jbrazio/arduheater/arduheater/console.h

/**
 * Arduheater - An intelligent dew buster for astronomy
 * Copyright (C) 2016-2019 João Brázio [joao@brazio.org]
 *
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
 */

#ifndef __LOG_H__
#define __LOG_H__

#include <stdint.h>
#include <stdlib.h>

#include "version.h"
#include "config.h"

#include <avr/pgmspace.h>

#include "serial.h"

// Special characters
const char string_colon   [] PROGMEM = { 0x3a, 0x00 };
const char string_comma   [] PROGMEM = { 0x2c, 0x00 };
const char string_eol     [] PROGMEM = { 0x0a, 0x00 };
const char string_minus   [] PROGMEM = { 0x2d, 0x00 };
const char string_percent [] PROGMEM = { 0x25, 0x00 };
const char string_space   [] PROGMEM = { 0x20, 0x00 };
const char string_zero    [] PROGMEM = { 0x30, 0x00 };

class Log
{
  /**
   * Disable the creation of an instance of this object.
   * This class should be used as a static class.
   */
  private:
     Log() {;}
    ~Log() {;}

  public:
    static void eol()   { Log::PGM(string_eol); }
    static void space() { Log::PGM(string_space); }
    static void comma() { Log::PGM(string_comma); }
    static void colon() { Log::PGM(string_colon); }
    static void minus() { Log::PGM(string_minus); }
    static void zero()  { Log::PGM(string_zero); }

  public:
    inline static void string(const char* s)
    {
      while (*s)
        Serial::write(*s++);
    }

    inline static void PGM(const char* s)
    {
      char c;
      while ((c = pgm_read_byte(s++)))
        Serial::write(c);
    }

  public:
    // uint8: 0 to 255
    static void number(const uint8_t& n)
    {
      uint8_t digits = 3;
      if (n < 10) { digits = 1; }
      else if (n < 100) { digits = 2; }
      Log::number(n, 10, digits);
    }

    // int8: -127 to 127
    static void number(const int8_t& n)
    {
      if (n < 0) {
        Log::minus();
        Log::number(-n, 10);
      } else Log::number(n);
    }

    // uint16: 0 to 65535
    static void number(const uint16_t& n)
    {
      Log::number(n, 10);
    }

    // int16: -32768 to 32767
    static void number(const int16_t& n)
    {
      if (n < 0) {
        Log::minus();
        Log::number(-n, 10);
      } else Log::number(n, 10);
    }

    // uint32: 0 to 4294967295L
    static void number(const uint32_t& n)
    {
      Log::number(n, 10);
    }

    // int32: -2147483648L to 2147483647L
    static void number(const int32_t& n)
    {
      if (n < 0) {
        Log::minus();
        Log::number(-n, 10);
      } else Log::number(n, 10);
    }

    // float:
    static void number(const float& n)
    {
      Log::fraq(n, 2);
    }

  public:
    static void binary(const uint8_t& n)  { Log::number(n, 2, 8); }
    static void binary(const int8_t& n)   { Log::number(n, 2, 8); }
    static void binary(const uint16_t& n) { Log::number(n, 2, 16); }
    static void binary(const int16_t& n)  { Log::number(n, 2, 16); }
    static void binary(const uint32_t& n) { Log::number(n, 2, 32); }
    static void binary(const int32_t& n)  { Log::number(n, 2, 32); }

  protected:
    static void number(uint32_t n, const uint8_t& base, const uint8_t& digits)
    {
      uint8_t i = 0;
      unsigned char buf[digits];

      for (; i < digits; i++) {
        buf[i] = n % base;
        n /= base;
      }

      for (; i > 0; i--) {
        if (i < digits && base == 2 && !((digits - i) % 4)) Log::space();
        Serial::write('0' + buf[i - 1]);
      }
    }

    static void number(const uint32_t& n, const uint8_t& base)
    {
      if (!n) {
        Log::zero();
        return;
      }

      uint32_t c = n;
      uint8_t digits = 0;
      while (c) { c /= 10; digits++; }
      Log::number(n, base, digits);
    }

    static void fraq(float n, const uint8_t& decimal_places)
    {
      if (n < 0) {
        Log::minus();
        n = -n;
      }

      uint8_t decimals = decimal_places;

      // Quickly convert values expected to be E0 to E-4.
      while (decimals >= 2) {
        n *= 100;
        decimals -= 2;
      }

      if (decimals) { n *= 10; }
      n += 0.5; // Add rounding factor. Ensures carryover through entire value.

      // Generate digits backwards and store in string.
      unsigned char buf[10];
      uint8_t i = 0;
      uint32_t a = (long)n;

      // Place decimal point, even if decimal places are zero.
      buf[decimal_places] = '.';

      while(a > 0) {
        if (i == decimal_places) { i++; } // Skip decimal point location
        buf[i++] = (a % 10) + '0'; // Get digit
        a /= 10;
      }

      // Fill in zeros to decimal point for (n < 1)
      while (i < decimal_places)
        buf[i++] = '0';

      // Fill in leading zero, if needed.
      if (i == decimal_places) {
        i++;
        buf[i++] = '0';
      }

      // Console the generated string.
      for (; i > 0; i--)
        Serial::write(buf[i-1]);
    }
};

class LogLn
{
  /**
   * Disable the creation of an instance of this object.
   * This class should be used as a static class.
   */
  private:
     LogLn() {;}
    ~LogLn() {;}

  public:
    inline static void string(const char* s) { Log::string(s); Log::eol(); }
    inline static void PGM(const char* s)    { Log::PGM(s); Log::eol();    }

  public:
    static void number(const uint8_t& n)  { Log::number(n); Log::eol(); }
    static void number(const int8_t& n)   { Log::number(n); Log::eol(); }
    static void number(const uint16_t& n) { Log::number(n); Log::eol(); }
    static void number(const int16_t& n)  { Log::number(n); Log::eol(); }
    static void number(const uint32_t& n) { Log::number(n); Log::eol(); }
    static void number(const int32_t& n)  { Log::number(n); Log::eol(); }
    static void number(const float& n)    { Log::number(n); Log::eol(); }
/*
  public:
    static void binary(const uint8_t& n)  { Log::binary(n); Log::eol(); }
    static void binary(const int8_t& n)   { Log::binary(n); Log::eol(); }
    static void binary(const uint16_t& n) { Log::binary(n); Log::eol(); }
    static void binary(const int16_t& n)  { Log::number(n); Log::eol(); }
    static void binary(const uint32_t& n) { Log::binary(n); Log::eol(); }
    static void binary(const int32_t& n)  { Log::binary(n); Log::eol(); }
*/
};

#endif
