jbrazio/arduheater/arduheater/io.h

/**
 * Arduheater - An intelligent dew buster for astronomy
 * Copyright (C) 2016-2019 João Brázio [joao@brazio.org]
 *
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
 */

#ifndef __IO_H__
#define __IO_H__

#include <stdint.h>
#include <stdlib.h>

#include "version.h"
#include "config.h"

#include "hal.h"
#include "log.h"
#include "macro.h"

#define LOW 0
#define HIGH 255

class IO
{
  /**
   * Disable the creation of an instance of this object.
   * This class should be used as a static class.
   */
  private:
     IO() {;}
    ~IO() {;}

  public:
    inline static void set_as_input(const uint8_t &pin) {
      const uint8_t     mask = pgm_read_word(&pin_map[pin][HALPIN]);
      volatile uint8_t *mode = (volatile uint8_t *)(pgm_read_word(&pin_map[pin][HALDIR]));
      volatile uint8_t *port = (volatile uint8_t *)(pgm_read_word(&pin_map[pin][HALOUT]));

      CRITICAL_SECTION_START
      *mode &= ~mask;
      *port &= ~mask;
      CRITICAL_SECTION_END
    }

    inline static void set_as_output(const uint8_t &pin) {
      const uint8_t     mask = pgm_read_word(&pin_map[pin][HALPIN]);
      volatile uint8_t *mode = (volatile uint8_t *)(pgm_read_word(&pin_map[pin][HALDIR]));

      CRITICAL_SECTION_START
      *mode |= mask;
      CRITICAL_SECTION_END
    }

    inline static void write(const uint8_t &pin, const uint8_t &value) {
      const uint8_t timer = pgm_read_byte(&pin_map[pin][HALTMR]);

      // Deals with digital signals i.e. LOW and HIGH
      if(value == LOW || value == HIGH) {

        const uint8_t     mask = pgm_read_word(&pin_map[pin][HALPIN]);
        volatile uint8_t *port = (volatile uint8_t *)( pgm_read_word(&pin_map[pin][HALOUT]) );

        // Turns off any active PWM output on the pin
        switch(timer)
        {
          case TIMER0A: cbi(TCCR0A, COM0A1); break; // timer 0, channel A
          case TIMER0B: cbi(TCCR0A, COM0B1); break; // timer 0, channel B
          case TIMER1A: cbi(TCCR1A, COM1A1); break; // timer 1, channel A
          case TIMER1B: cbi(TCCR1A, COM1B1); break; // timer 1, channel B
          case TIMER2A: cbi(TCCR2A, COM2A1); break; // timer 2, channel A
          case TIMER2B: cbi(TCCR2A, COM2B1); break; // timer 2, channel B
          default: ;
        }

        CRITICAL_SECTION_START
        if(value == LOW) { *port &= ~mask; }
        else { *port |= mask; }
        CRITICAL_SECTION_END
      }

      // Deals with analog signals i.e. PWM
      else {
        switch(timer)
        {
          case TIMER0A: sbi(TCCR0A, COM0A1); OCR0A = value; break; // timer 0, channel A
          case TIMER0B: sbi(TCCR0A, COM0B1); OCR0B = value; break; // timer 0, channel B
          case TIMER1A: sbi(TCCR1A, COM1A1); OCR1A = value; break; // timer 1, channel A
          case TIMER1B: sbi(TCCR1A, COM1B1); OCR1B = value; break; // timer 1, channel B
          case TIMER2A: sbi(TCCR2A, COM2A1); OCR2A = value; break; // timer 2, channel A
          case TIMER2B: sbi(TCCR2A, COM2B1); OCR2B = value; break; // timer 2, channel B
          default: write(pin, (value < 128) ? 0 : 255); // fallbacks to digital mode
        }
      }
    }

    inline static uint8_t read(const uint8_t &pin) {
        const uint8_t     mask  = pgm_read_word(&pin_map[pin][HALPIN]);
        const uint8_t     timer = pgm_read_byte(&pin_map[pin][HALTMR]);
        volatile uint8_t *port  = (volatile uint8_t *)(pgm_read_word(&pin_map[pin][HALIN]));

        // If the pin that support PWM output, we need to turn it off
        // before getting a digital reading.
        if (timer != NOTIMER) {
          switch(timer)
          {
            case TIMER0A: cbi(TCCR0A, COM0A1); break; // timer 0, channel A
            case TIMER0B: cbi(TCCR0A, COM0B1); break; // timer 0, channel B
            case TIMER1A: cbi(TCCR1A, COM1A1); break; // timer 1, channel A
            case TIMER1B: cbi(TCCR1A, COM1B1); break; // timer 1, channel B
            case TIMER2A: cbi(TCCR2A, COM2A1); break; // timer 2, channel A
            case TIMER2B: cbi(TCCR2A, COM2B1); break; // timer 2, channel B
            default: ;
          }
        }

        if (*port & mask) return HIGH;
        return LOW;
    }
};

#endif
