jbrazio/arduheater/arduheater/serial.cpp

/**
 * Arduheater - An intelligent dew buster for astronomy
 * Copyright (C) 2016-2019 João Brázio [joao@brazio.org]
 *
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
 */

#include "serial.h"

/**
 * @brief Static class member initialization
 */
Serial::buffer_t Serial::s_buffer;

/**
 * @brief USART RX interrupt handler
 */
#ifdef __AVR_ATmega328PB__
  ISR(USART0_RX_vect)
#else
  ISR(USART_RX_vect)
#endif
{
  // read a byte from the incoming stream
  char c = UDR0;

  // check for parity error
  if (bit_is_clear(UCSR0A, UPE0)) {
    Serial::s_buffer.rx.enqueue(c);
  } /* else { discard byte } */
}

/**
 * @brief USART TX interrupt handler
 */
#ifdef __AVR_ATmega328PB__
  ISR(USART0_UDRE_vect)
#else
  ISR(USART_UDRE_vect)
#endif
  {
  // turn off Data Register Empty Interrupt
  // to stop tx-streaming if this concludes the transfer
  if (Serial::s_buffer.tx.empty()) { UCSR0B &= ~bit(UDRIE0); }

  else {
    // send a byte from the buffer
    UDR0 = Serial::s_buffer.tx.dequeue();
    UCSR0A |= bit(TXC0);
  }
}

/**
 * @brief Checks if the RX queue has data
 * @return Boolean value representing the state of the RX queue
 */
bool Serial::available()
{
  return (! Serial::s_buffer.rx.empty());
}

/**
 * @brief Read a char from the RX queue
 * @return A byte (char) from the queue
 */
char Serial::read()
{
  CRITICAL_SECTION_START
    const char c = (Serial::s_buffer.rx.empty()) ? 0XFF : Serial::s_buffer.rx.dequeue();
  CRITICAL_SECTION_END

  return c;
}

/**
 * @brief Flushes the TX queue
 */
void Serial::flush()
{
  CRITICAL_SECTION_START
    while (bit_is_set(UCSR0B, UDRIE0) || bit_is_clear(UCSR0A, TXC0))
    {
      if (bit_is_clear(SREG, SREG_I) && bit_is_set(UCSR0B, UDRIE0)) {
        if (bit_is_set(UCSR0A, UDRE0)) {
          // send a byte from the buffer
          UDR0 = Serial::s_buffer.tx.dequeue();
          UCSR0A |= bit(TXC0);

          // turn off Data Register Empty Interrupt
          // to stop tx-streaming if this concludes the transfer
          if (Serial::s_buffer.tx.empty()) { UCSR0B &= ~bit(UDRIE0); }
        }
      }
    }
  CRITICAL_SECTION_END
}

/**
 * @brief Parses the incoming byte stream, should only be used by the ISR
 */
void Serial::process(callbackfunc_t callback)
{

  static size_t pos = 0;
  static char   cmd[32];

  while(available())
  {
    char c = read();

    switch(c) {
      case '\r': // ignore windows line ending
        break;

      case '\n': // process the data on the buffer sent by an human
      case '#':  // process the data on the buffer
        callback(cmd);

      case ':':  // clears the data on the buffer
        memset(&cmd, 0, sizeof(cmd));
        pos = 0;
        break;

      default:   // adds data to the buffer
        cmd[pos++] = c;
        pos %= sizeof(cmd);
        break;
    }
  }
}

/**
 * @brief Initializes the USART
 */
void Serial::setup()
{
  CRITICAL_SECTION_START
    // Defines the speed at which the serial line will operate.
    // The default settings are: 8-bit, no parity, 1 stop bit.
    const uint16_t UBRR0_value = ((F_CPU / (4L * 57600)) - 1) /2;
    UCSR0A |= bit(U2X0);  // baud doubler on for high baud rates

    // set baudrate
    UBRR0H = UBRR0_value >> 8;
    UBRR0L = UBRR0_value;

    // enable rx and tx
    UCSR0B |= bit(RXEN0);
    UCSR0B |= bit(TXEN0);

    // enable interrupt on complete reception of a byte
    UCSR0B |= bit(RXCIE0);
  CRITICAL_SECTION_END
}

/**
 * @brief Adds a byte to the TX queue when free space is available
 * @details Take note this method can block program flow when the queue is full
 */
void Serial::write(const char& c)
{
  // wait until there is space in the buffer
  while (!Serial::s_buffer.tx.enqueue(c)) Serial::flush();

  // Enable Data Register Empty Interrupt
  // to make sure tx-streaming is running
  UCSR0B |= bit(UDRIE0);
}
