jbrazio/arduheater/src/runtime.cpp

/**
 * Arduheater - Telescope heat controller
 * Copyright (C) 2016-2017 João Brázio [joao@brazio.org]
 *
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
 */

#include "common.h"

void runtime::update(const message_t& message) {
  switch (message.category) {
    case MSG_CAT_KEYPAD: {
      DEBUGPRN(3, "runtime::update(): MSG_CAT_KEYPAD");

      #if defined(VERBOSE) && VERBOSE >= 3
      keycode_t  button = static_cast<keycode_t>(message.data[0].dw);
      keypress_t state  = static_cast<keypress_t>(message.data[1].dw);

      serial::print::PGM(PSTR("buton("));
      serial::print::uint8(button);
      serial::print::PGM(PSTR("): "));
      serial::println::uint8(state);
      #endif

      /*if (runtime::single::instance().heater[0].running()) {
        runtime::single::instance().heater[0].off();
      } else {
        runtime::single::instance().heater[0].on();
      }*/

      ui::single::instance().update(message);
      break;
    }

    case MSG_CAT_WEATHER: {
      DEBUGPRN(6, "runtime::update(): MSG_CAT_WEATHER");

      #if defined(VERBOSE) && VERBOSE >= 6
      serial::print::PGM(PSTR("MSG_CAT_WEATHER: t: "));
      serial::print::float32(message.data[0].f, 2);
      serial::print::PGM(PSTR(", rh: "));
      serial::print::float32(message.data[1].f, 2);
      serial::print::PGM(PSTR(", dew: "));
      serial::println::float32(utils::weather::dew(message.data[0].f, message.data[1].f), 2);
      #endif

      ambient.t   += roundf(message.data[0].f);
      ambient.rh  += roundf(message.data[1].f);
      ambient.dew += roundf(utils::weather::dew(message.data[0].f, message.data[1].f));

      static int8_t t, rh, dew; // cache values
      if ((ambient.t() != t) || (ambient.rh() != rh) || (ambient.dew() != dew)) {
        t   = ambient.t();
        rh  = ambient.rh();
        dew = ambient.dew();

        ui::single::instance().update({MSG_UPDATE_LCD, 0});
      }
      break;
    }

    case MSG_CAT_NTC: {
      DEBUGPRN(6, "runtime::update(): MSG_CAT_NTC");

      #if defined(VERBOSE) && VERBOSE >= 6
      serial::print::PGM(PSTR("MSG_CAT_NTC: channel: "));
      serial::print::uint8(message.data[0].ub[0]);
      serial::print::PGM(PSTR(", t: "));
      serial::println::float32(message.data[1].f, 2);
      #endif

      uint8_t ch = message.data[0].ub[0];
      heater[ch].t += roundf(message.data[1].f);

      static int16_t t[4]; // cache values

      if (heater[ch].t() != t[ch]) {
        t[ch] = heater[ch].t();
        ui::single::instance().update({MSG_UPDATE_LCD, 0});
      }
      break;
    }

    default: { break; }
  }
}
