jbrazio/arduheater/arduheater/utility.cpp

/**
 * Arduheater - An intelligent dew buster for astronomy
 * Copyright (C) 2016-2019 João Brázio [joao@brazio.org]
 *
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
 */

#include "utility.h"

/**
 * @brief [brief description]
 * @details [long description]
 *
 */
float calculate_dew(const float& t, const float& rh)
{
  // Uncomment the following line to enable the NOAA dew function
  // otherwise a simpler calculating algorithm will be used.
  //#define USE_NOAA_DEW_FUNCTION

  #ifdef USE_NOAA_DEW_FUNCTION
    // dewPoint function NOAA
    // reference (1) : http://wahiduddin.net/calc/density_algorithms.htm
    // reference (2) : http://www.colorado.edu/geography/weather_station/Geog_site/about.htm

    // (1) Saturation Vapor Pressure = ESGG(T)
    const float RATIO = 373.15 / (273.15 + t);
    float RHS = -7.90298 * (RATIO - 1);
    RHS += 5.02808 * log10(RATIO);
    RHS += -1.3816e-7 * (pow(10, (11.344 * (1 - 1/RATIO ))) - 1) ;
    RHS += 8.1328e-3 * (pow(10, (-3.49149 * (RATIO - 1))) - 1) ;
    RHS += log10(1013.246);

    // factor -3 is to adjust units - Vapor Pressure SVP * rh
    const float VP = pow(10, RHS - 3) * rh;

    // (2) DEWPOINT = F(Vapor Pressure)
    const float T = log(VP/0.61078);   // temp var
    return (241.88 * T) / (17.558 - T);
  #else
    // delta max = 0.6544 wrt dewPoint()
    // 6.9 x faster than dewPoint function NOAA
    // reference: http://en.wikipedia.org/wiki/Dew_point
    const float temp = (17.271f * t) / (237.7f + t) + log(rh * 0.01);
    return (237.7f * temp) / (17.271f - temp);
  #endif
}
